nic6911/Wavin-AHC-9000-mqtt/electronics/Bottom.PNG

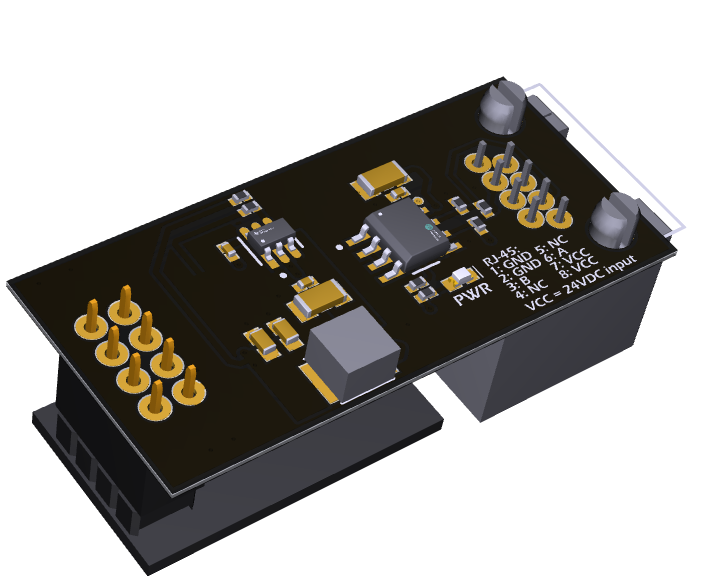
electronics/Bottom.PNG
