nic6911/Wavin-AHC-9000-mqtt/electronics/schematic.png

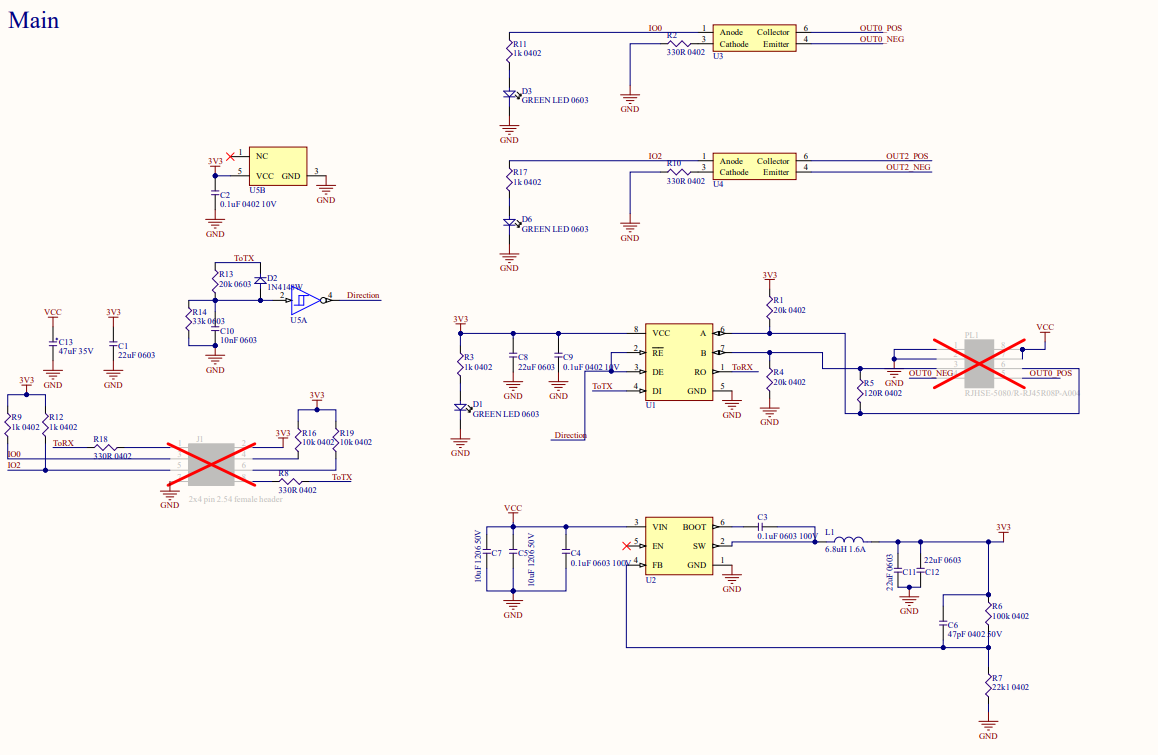
electronics/schematic.png
