nic6911/Wavin-AHC-9000-mqtt/software/ESP8266/Arduino/OTA/AP.png

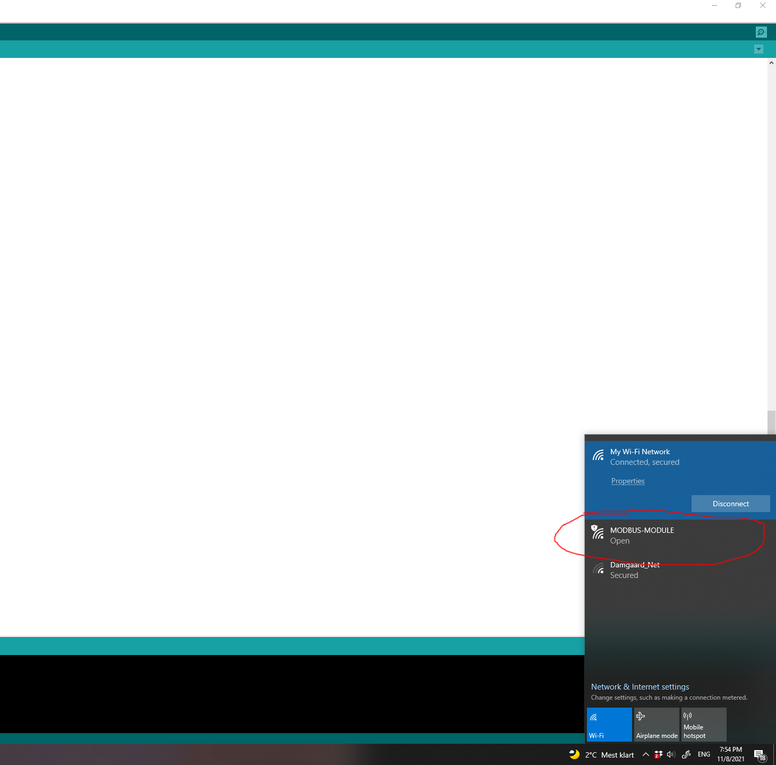
software/ESP8266/Arduino/OTA/AP.png
