nic6911/Wavin-AHC-9000-mqtt/software/ESP8266/Arduino/OTA/mqttwifisetting.PNG

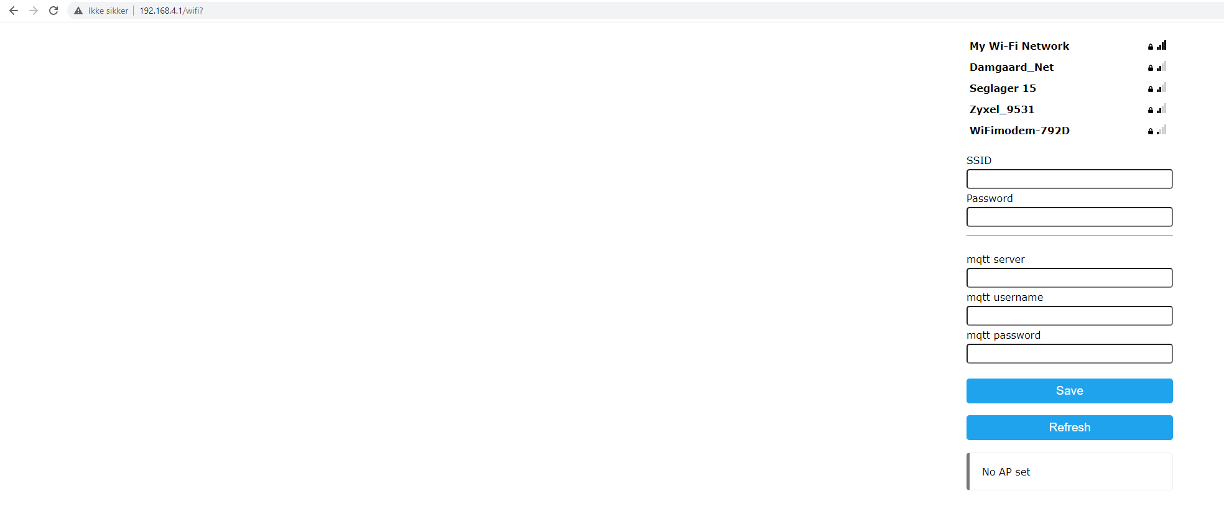
software/ESP8266/Arduino/OTA/mqttwifisetting.PNG
