nic6911/Wavin-AHC-9000-mqtt/software/ESP8266/Arduino/OTA/wifi_setting.png

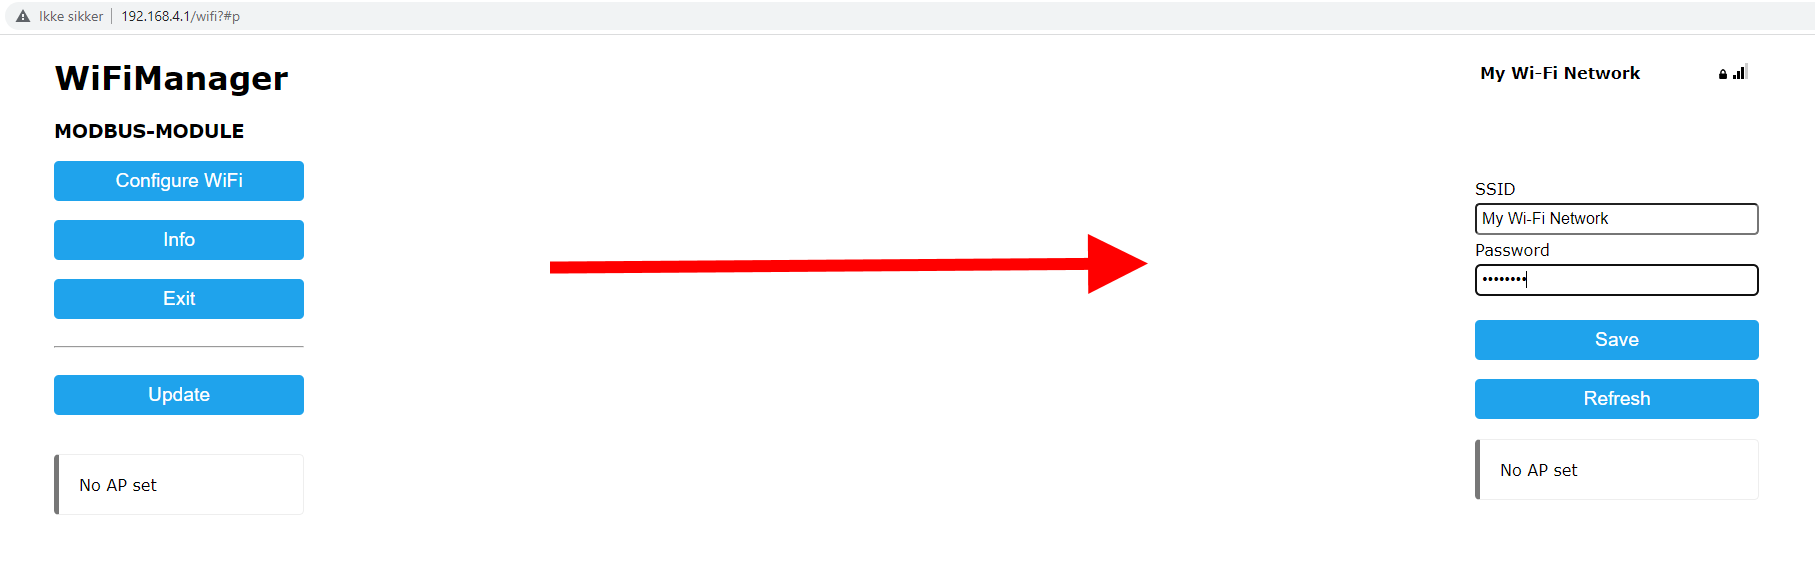
software/ESP8266/Arduino/OTA/wifi_setting.png
