nic6911/Wavin-AHC-9000-mqtt/software/ESP32C3/Arduino/wavin/PrivateConfig.h

#include <WiFi.h>

// MQTT settings
#define MQTTSERVER   "192.168.1.105" // Put in the IP adresse of your MQTT broker
#define MQTTUSERNAME "homey" // User name for the MQTT broker (NULL if no user name is required)
#define MQTTPASSWORD "homey" // Password for the MQTT broker (NULL if no password is required)
