nic6911/Wavin-AHC-9000-mqtt/software/ESP8266/Arduino/wavin/PrivateConfig.h

#include <ESP8266WiFi.h>

// MQTT settings
#define MQTTSERVER   "192.168.0.100" // Put in the IP adresse of your MQTT broker
#define MQTTUSERNAME "user" // User name for the MQTT broker (NULL if no user name is required)
#define MQTTPASSWORD "pass" // Password for the MQTT broker (NULL if no password is required)
